MrColoo/DJI-Ronin-Remote-Controller-ESP32-ESP8266/Image Gallery/device-overview-1.jpg

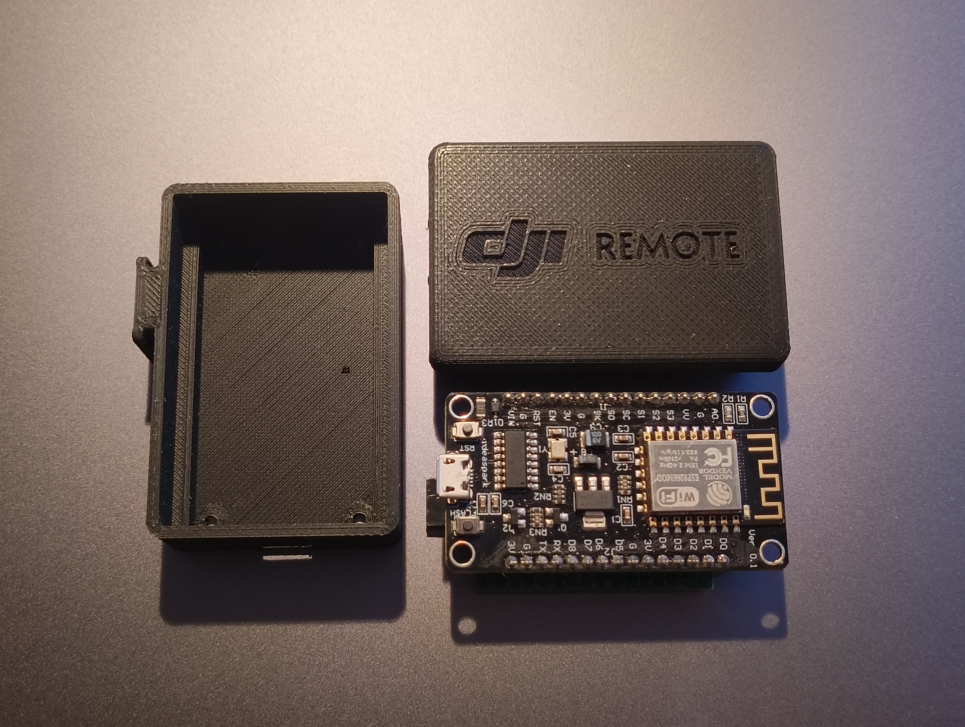
Image Gallery/device-overview-1.jpg
