MrColoo/DJI-Ronin-Remote-Controller-ESP32-ESP8266/Image Gallery/full-overview-4.jpg

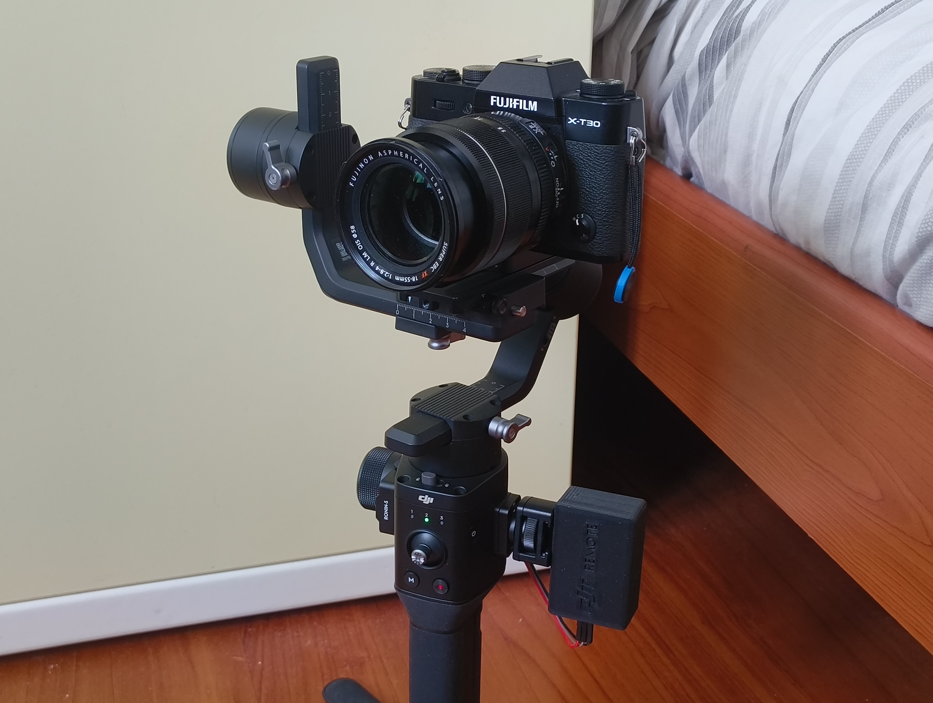
Image Gallery/full-overview-4.jpg
