MrColoo/DJI-Ronin-Remote-Controller-ESP32-ESP8266/Image Gallery/how-to-connect-3.jpg

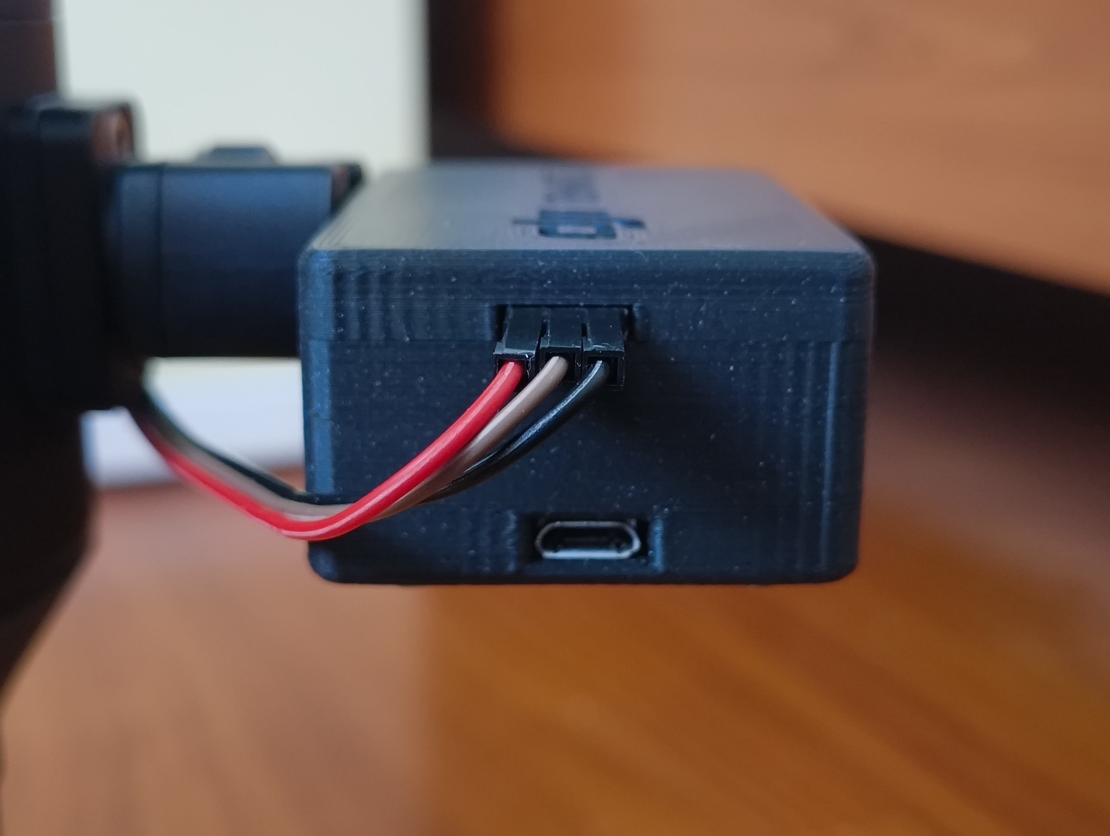
Image Gallery/how-to-connect-3.jpg
